Board-Folk/CPC464-2MINI/Expansions/MINIDDI/Extras/MINIDDI3ADAPT/README.md

# MINIDDI3ADAPT

Adapter for 3" drives for the MINIDDI Expansion

# BOM

* There are no components on this board.
