Board-Folk/CPC464-2MINI/Expansions/MINIPS2/Arduino/AMS_keyboard/keymapping.h

typedef struct {
  uint8_t noshift_1[AMS_KEYMAP_SIZE];
  uint8_t shift_1[AMS_KEYMAP_SIZE];
  uint8_t noshift_2[AMS_KEYMAP_SIZE];
  uint8_t shift_2[AMS_KEYMAP_SIZE];
} AMSKeymap_t;

/* Maps are positional in relation to keyboard ASCII codes.

Each map has a normal (without shift) and shifted (with shift) array.

In situations where there is a shift difference, add 80 to the Amstrad key byte. 
This is when a key is shifted on keyboard, but not shifted on the Amstrad or vise-versa.

Unused ASCII codes need to have the IGNORE_KEYCODE value in place.(Default 170)

*/

#if defined(CPC464)

// CPC464

const PROGMEM AMSKeymap_t AMSKeymap_main = {
  // map 1 without shift
   {170,170,170,  3,170,170, 29, 29,// ASCII Codes 0x00 - 0x07
     31, 31,170,170, 60,170,170,170,// ASCII Codes 0x08 - 0x0F
    170,170,170,170,170, 56, 68, 64,// ASCII Codes 0x10 - 0x17
     66,170,170,  2, 79,  1, 26, 55,// ASCII Codes 0x18 - 0x1F
     63, 61, 59, 69, 25, 57, 65, 58,// ASCII Codes 0x20 - 0x27
     62, 70, 71, 67,170,170,170,170,// ASCII Codes 0x28 - 0x2F
      8,  0,  4, 36, 32, 20, 16, 52,// ASCII Codes 0x30 - 0x37
     48, 12, 41, 15, 44, 47, 43,170,// ASCII Codes 0x38 - 0x3F
     24,  5, 19, 35, 37, 34, 21, 17,// ASCII Codes 0x40 - 0x47
     49, 14, 53, 13,  9, 11, 51, 10,// ASCII Codes 0x48 - 0x4F
     46,  6, 18, 33, 22, 50, 23, 38,// ASCII Codes 0x50 - 0x57
     39, 54,  7, 45, 30, 42, 28, 40,// ASCII Codes 0x58 - 0x5F
    170,170,170,170,170,170,170,170,// ASCII Codes 0x60 - 0x67
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
    170,170,170,170,170,170,170,170,// ASCII Codes 0x78 - 0x7F
    170,170,170,170,170,170,170,170,// ASCII Codes 0x78 - 0x7F
    170,170,170,170,170,170,170,170,// ASCII Codes 0x80 - 0x87      //erm.
    170,170,170,139,170,170,170,170},// ASCII Codes 0x88 - 0x8F 
    
}; 
#endif
